michelelizzit/phylab2.0/pcb/phylab_module_pcbv3/PCBv3_phylab_etch_silk_bottom.pdf

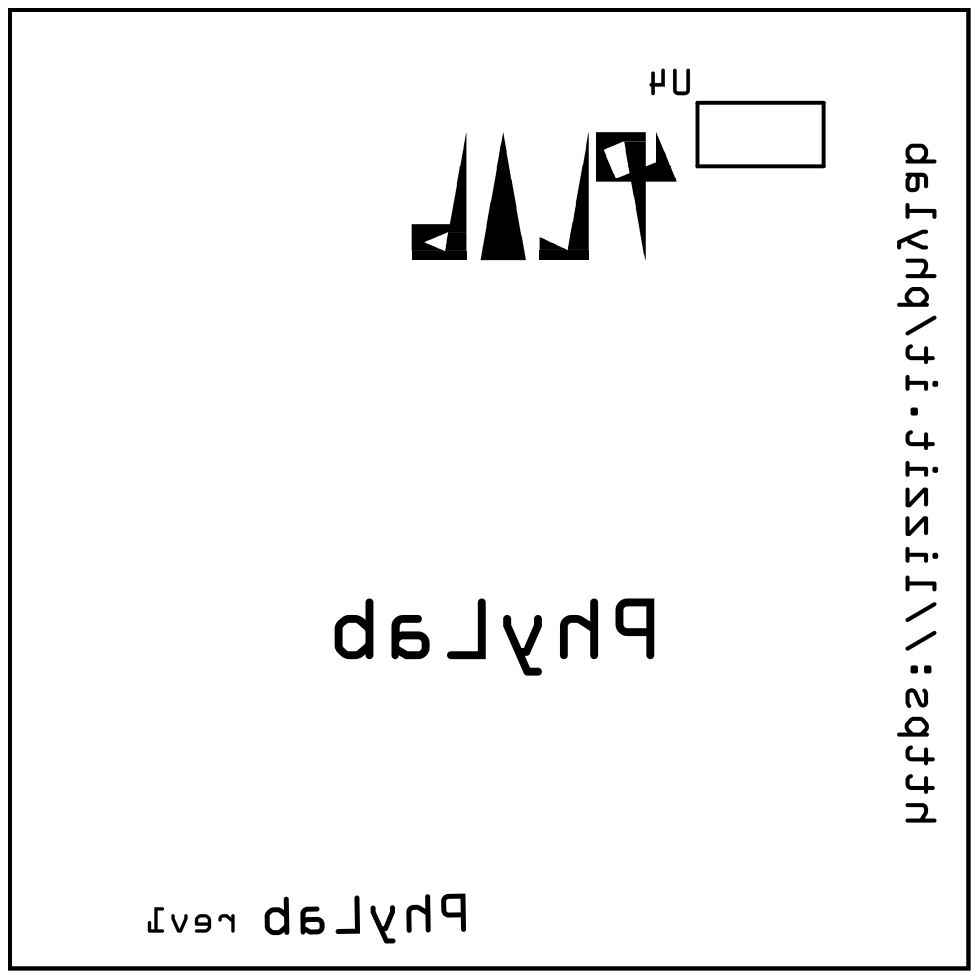
[picture p9: page 1]
