michelelizzit/phylab2.0/pcb/phylab_module_pcbv3/PCBv3_phylab_etch_silk_bottom_mirror.pdf

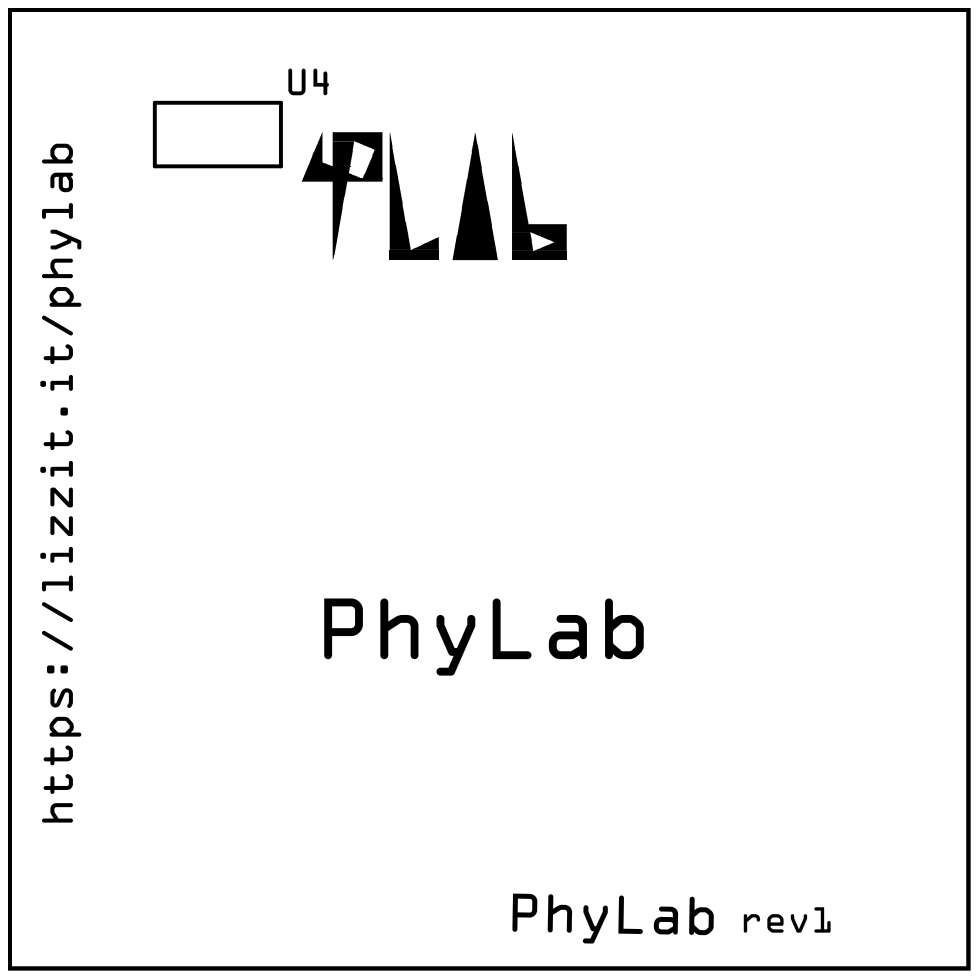
[picture p10: page 1]
