michelelizzit/phylab2.0/pcb/phylab_module_pcbv3/PCBv3_phylab_etch_silk_top.pdf

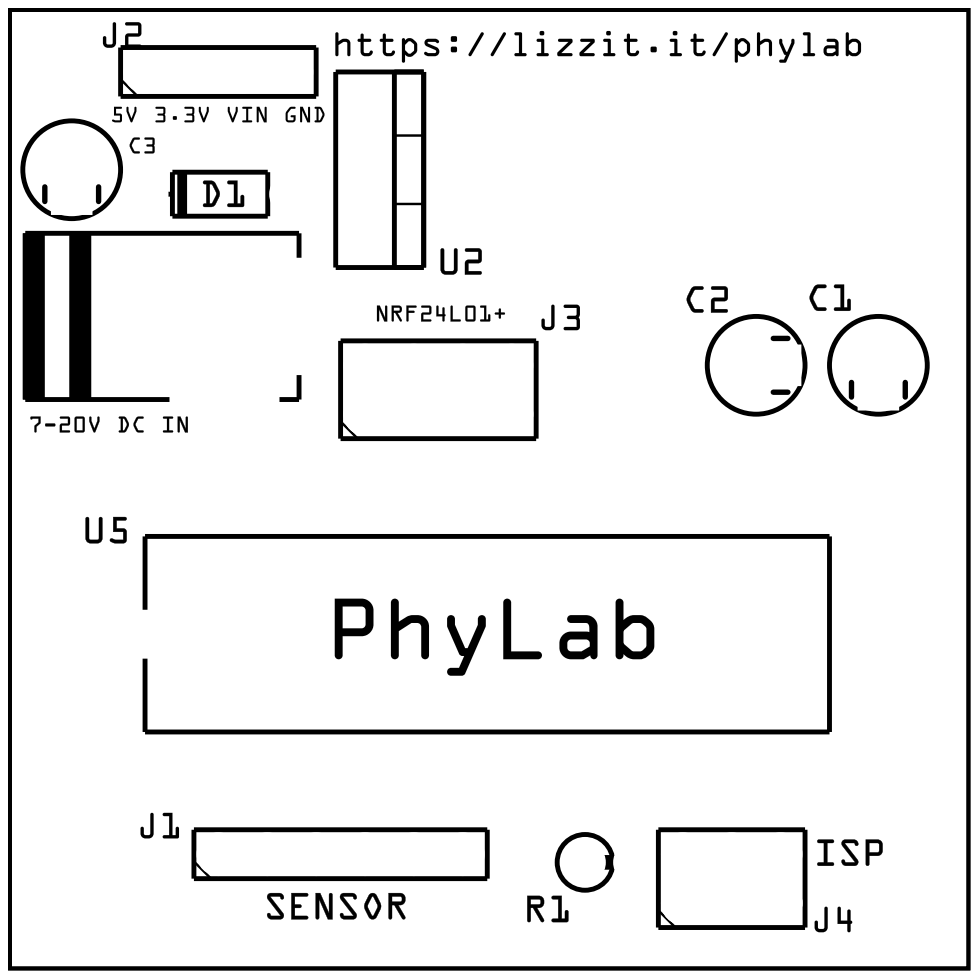
[picture p11: page 1]
