michelelizzit/phylab2.0/pcb/phylab_raspi_v1/raspi_phylab_v1_etch_copper_bottom_mirror.pdf

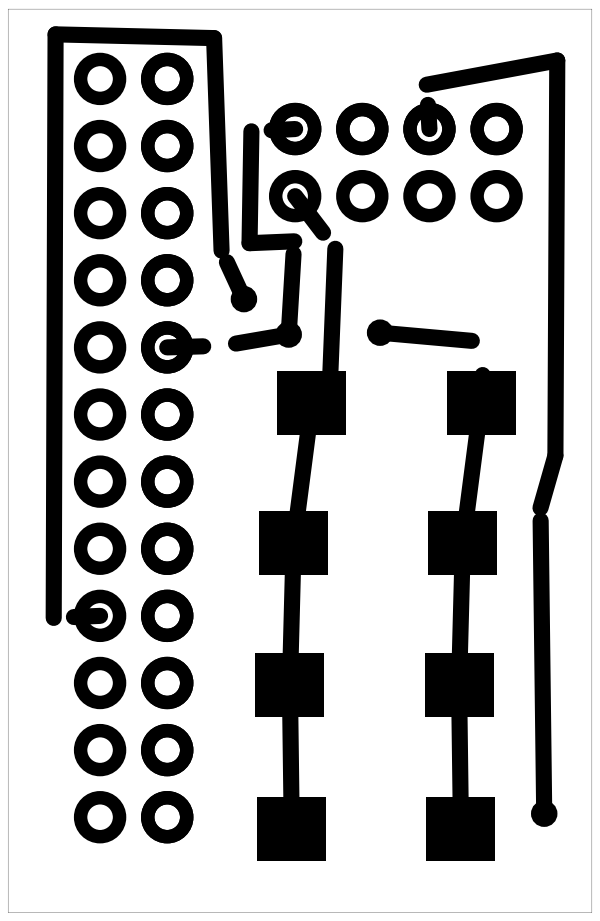
[picture p14: page 1]
