michelelizzit/phylab2.0/pcb/phylab_raspi_v1/raspi_phylab_v1_etch_copper_top_mirror.pdf

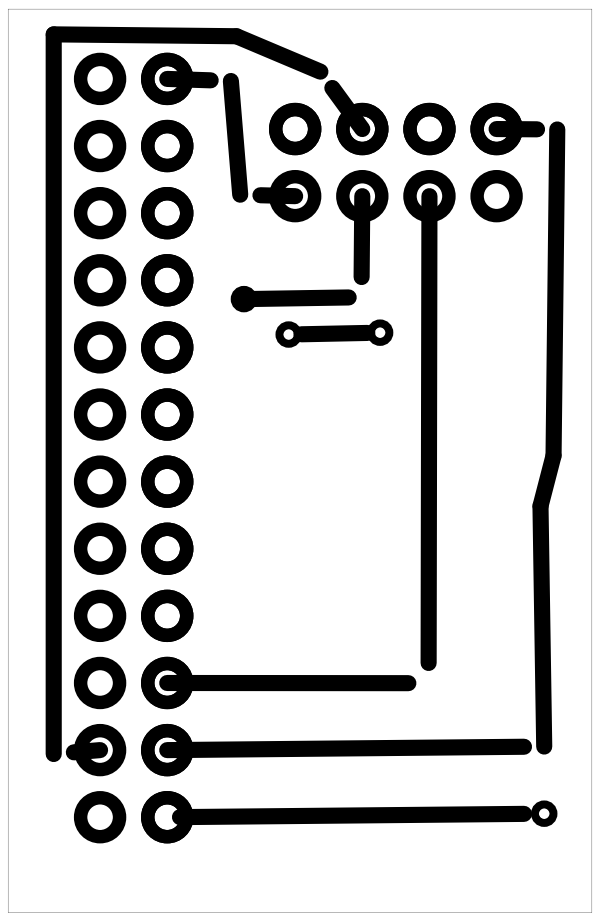
[picture p16: page 1]
