michelelizzit/phylab2.0/pcb/phylab_raspi_v1/raspi_phylab_v1_etch_mask_bottom.pdf

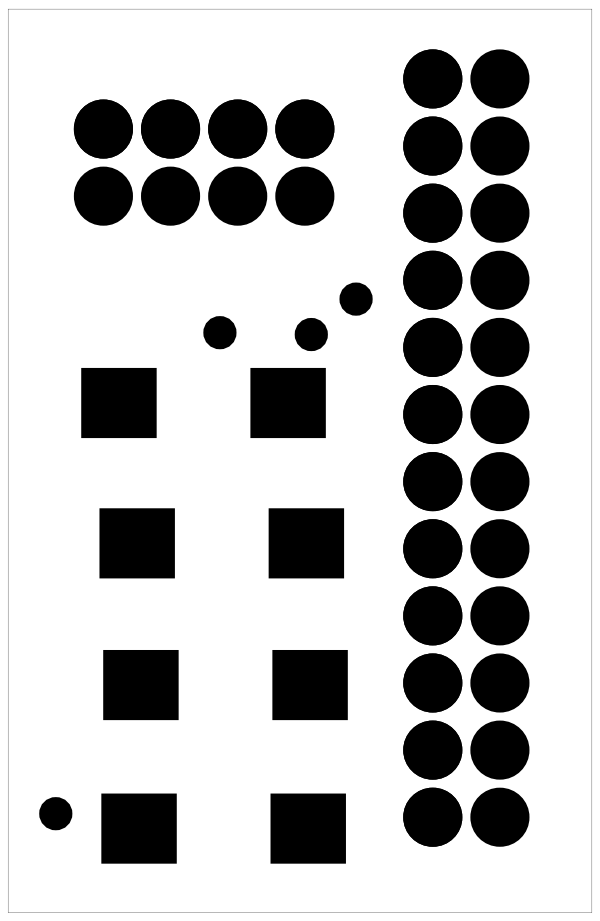
[picture p17: page 1]
