michelelizzit/phylab2.0/pcb/phylab_raspi_v1/raspi_phylab_v1_etch_mask_top.pdf

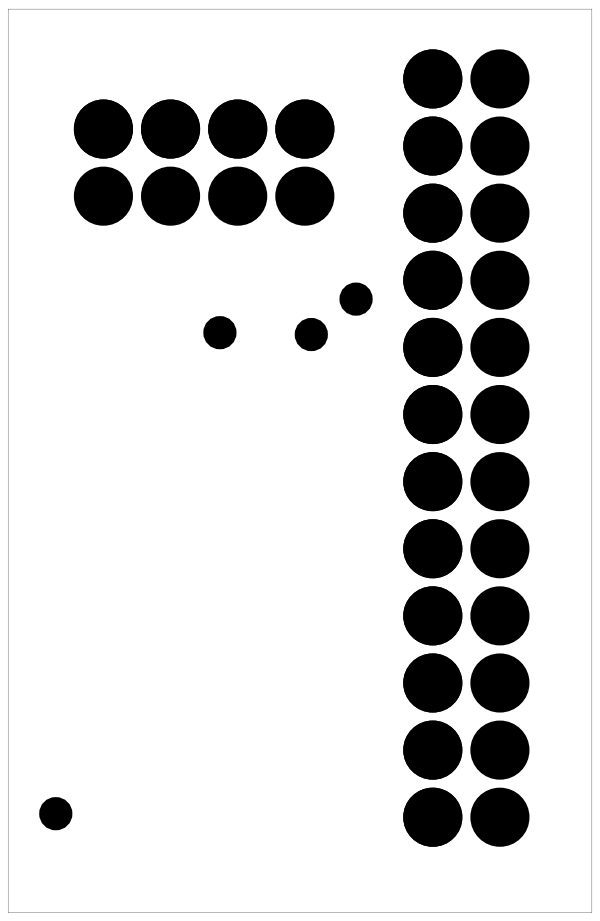
[picture p19: page 1]
