michelelizzit/phylab2.0/pcb/phylab_raspi_v1/raspi_phylab_v1_etch_mask_top_mirror.pdf

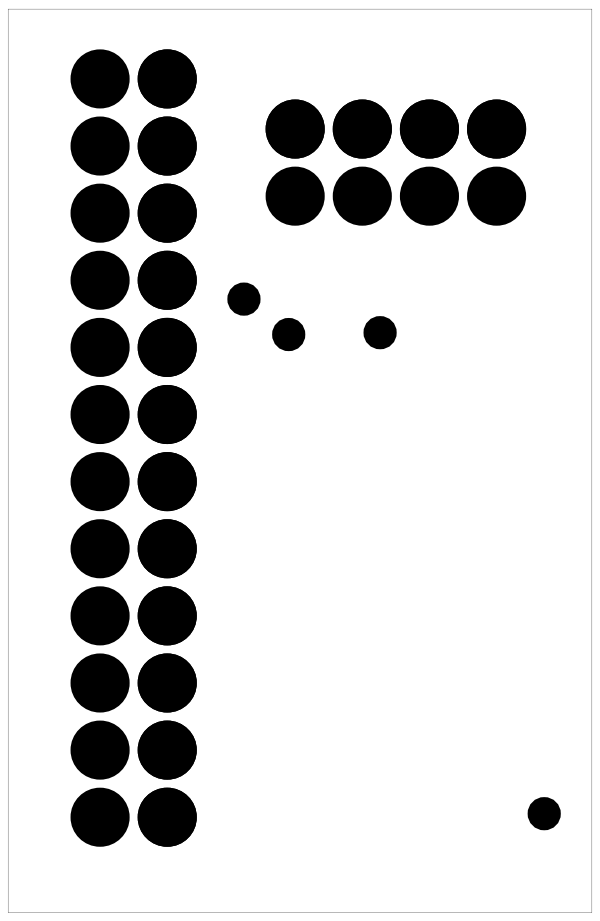
[picture p20: page 1]
