michelelizzit/phylab2.0/pcb/phylab_raspi_v1/raspi_phylab_v1_etch_silk_bottom.pdf

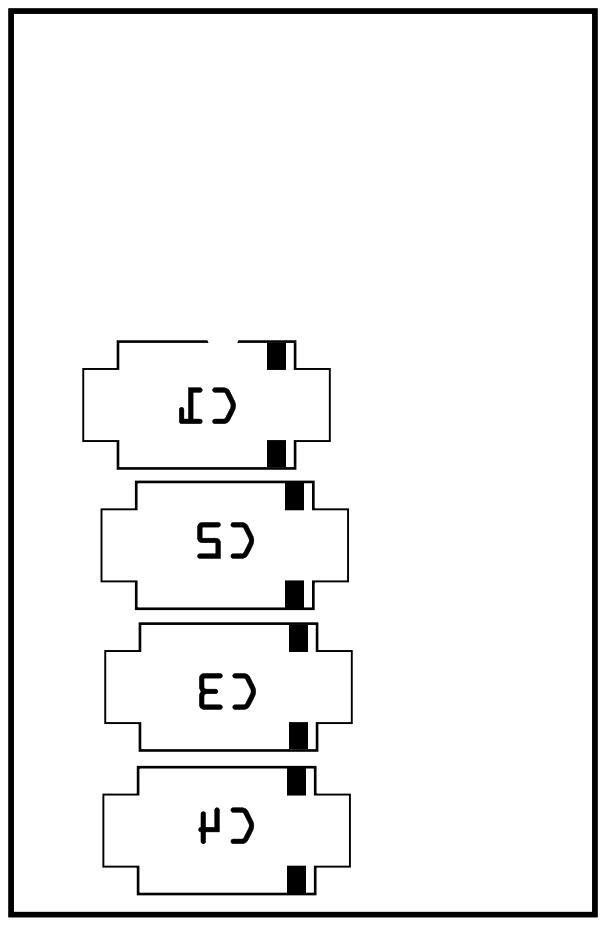
[picture p21: page 1]
