michelelizzit/phylab2.0/pcb/phylab_raspi_v1/raspi_phylab_v1_etch_silk_top.pdf

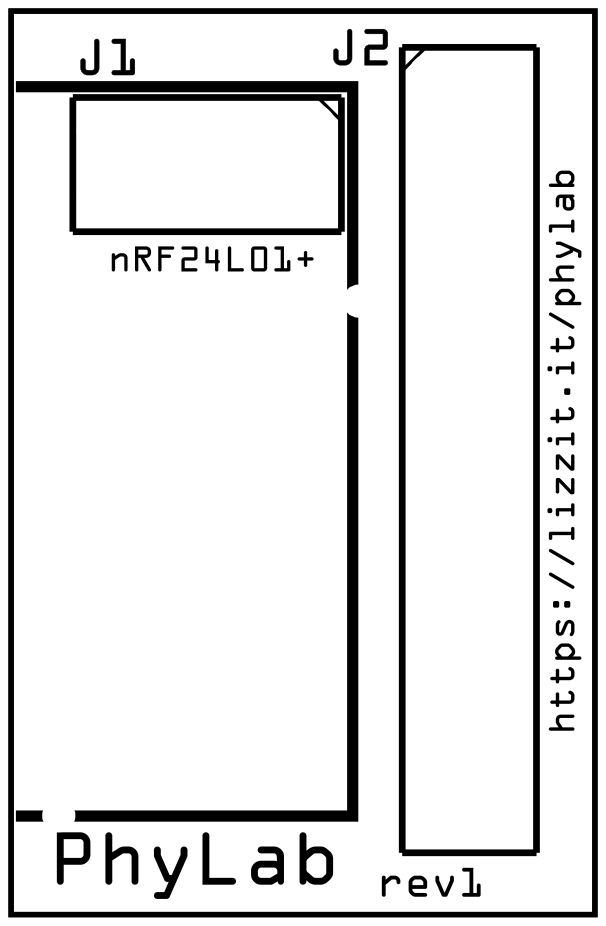
[picture p23: page 1]
