michelelizzit/phylab2.0/src/modules/phylab_acceleration_experiment_module_v1/Config.h

#define ACC_X_PIN A5 //A3
#define TARAX 0 //340


//Default CE is 8, CSN is 7
#define PIN_NRF_OVERRIDE_DEFAULT
#define CE_PIN A0
#define CSN_PIN A1

//Serial communication not implemented since
//this experiment requires the module to be
//connected wirelessly
